Blaze-Pascal/Eka-PGr-SignalGen/LtSpice/DAC.asc

R1: res; 1k
R2: res; 1k
R3: res; 1k
R4: res; 1k
R5: res; 1k
R6: res; 1k
R7: res; 1k
R8: res; 1k
R9: res; 2k
R10: res; 2k
R11: res; 2k
R12: res; 2k
R13: res; 2k
R14: res; 2k
R15: res; 2k
R16: res; 2k
R18: res; 1k
R19: res; 1k
R20: res; 1k
R21: res; 1k
R22: res; 1k
R23: res; 1k
U2: OP07
U3: OP07
V1: voltage; PULSE(0 3.3 0 1p 1p 10u 20u)
V2: voltage; PULSE(0 3.3 0 1p 1p 20u 40u)
V3: voltage; PULSE(0 3.3 0 1p 1p 40u 80u)
V4: voltage; PULSE(0 3.3 0 1p 1p 80u 160u)
V5: voltage; PULSE(0 3.3 0 1p 1p 160u 320u)
V6: voltage; PULSE(0 3.3 0 1p 1p 320u 640u)
V7: voltage; PULSE(0 3.3 0 1p 1p 640u 1280u)
V9: voltage; 10
V11: voltage; PULSE(0 3.3 0 1p 1p 1280u 2560u)
V12: voltage; PULSE(0 3.3 0 1p 1p 10u 20u)
V13: voltage; PULSE(0 3.3 0 1p 1p 20u 40u)
V14: voltage; PULSE(0 3.3 0 1p 1p 40u 80u)
V15: voltage; PULSE(0 3.3 0 1p 1p 80u 160u)
V16: voltage; PULSE(0 3.3 0 1p 1p 160u 320u)
V17: voltage; PULSE(0 3.3 0 1p 1p 320u 640u)
V18: voltage; PULSE(0 3.3 0 1p 1p 640u 1280u)
V19: voltage; PULSE(0 3.3 0 1p 1p 1280u 2560u)
V21: voltage; 1.65
Named nets: 0, v+, v-, Out
.tran 3000u
