Blaze-Pascal/Eka-PGr-SignalGen/LtSpice/Filter.asc

C1: cap; 10µ
C3: cap; 10µ
Q1: npn; BC547B
Q2: pnp; BC556B
R1: res; 1k
R2: res; 50
R4: res; 1k
R5: res; 50
V1: voltage; 11.5
V2: voltage; PULSE(0 1 0 5u 5u 0 10u)
V5: voltage; 11.5
V6: voltage; PULSE(0 1 0 5u 5u 0 10u)
Named nets: 0
.tran 100m
