Blaze-Pascal/Eka-PGr-SignalGen/LtSpice/Gensim.asc

C4: cap; 1000µ
C5: cap; 3.3p
C6: cap; 100n
C7: cap; 100n
D2: diode; 1N4148
D3: diode; 1N4148
Q1: npn
Q2: pnp
R1: res; 1k
R4: res; 20k
R5: res; 680
R6: res; 680
R8: res; 1k
R9: res; 1k
R10: res; 3.3
R11: res; 3.3
R15: res; 50
U2: OP07
V1: voltage; 12
V2: voltage; SINE(0 2 1k)
V3: voltage; 12
Named nets: 0, -12, 12
.tran 50m
